ensaminadin-pe/walker/walker_firmware/kinematic.h

#ifndef KINEMATIC_H
#define KINEMATIC_H

#include "types.h"

enum KinematicAxis : uint8
{
	KINEMATIC_AXIS_UNDEFINED = 0,
	KINEMATIC_AXIS_X,
	KINEMATIC_AXIS_Y,
	KINEMATIC_AXIS_Z,
};

#endif // KINEMATIC_H
