ensaminadin-pe/walker/walker_firmware/fabrik2d.cpp

/**********************************************************************************************
 * FABRIK 2D inverse kinematics solver - Version 1.0.0
 * by Henrik Söderlund <henrik.a.soderlund@gmail.com>
 *
 * Copyright (C) 2018 Henrik Söderlund
 *
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
 **********************************************************************************************/

#ifndef IS_QT
	#include "Arduino.h"
#else
	#include "arduinopolyfill.h"
	#include <math.h>
#endif
#include "fabrik2d.h"
#include "kinematic.h"
#include "config.h"
#include <stdio.h>
#include <stdlib.h>

Fabrik2D::Fabrik2D(float _tolerance)
{
	tolerance = _tolerance; //1mm
	joint_count = 0;
	chain_length = 0;
	joint_chain = NULL;
	joints_axis = KINEMATIC_AXIS_UNDEFINED;
}

Fabrik2D::~Fabrik2D()
{

}

/**
 * @brief Fabrik2D::addJoint Add a joint to the kinematic chain
 * @param joint
 * @return
 */
bool Fabrik2D::addJoint(WalkerJoint *joint)
{
	//1) Check that the chain exist
	if (!joint_chain)
	{ //Create chain and last point
		joint_chain = (WalkerJoint**)malloc(sizeof(WalkerJoint*));
		if (!joint_chain) // Could not allocate memory, error
			return false;
		WalkerJoint* last_joint = new WalkerJoint();
		if (!last_joint)
			return false;
		joint_chain[0] = last_joint;
		joint_count = 1;
	}

	//2) Check that joint can be added
	if (joints_axis != KINEMATIC_AXIS_UNDEFINED && joint->getAxis() != joints_axis)
		return false; //Cannot add a joint that doesnt rotate on the same axis as the others, this is 2D Fabrik
	joints_axis = joint->getAxis();

	//3) Resize joint chain
	uint8 joint_index = joint_count++ - 1;
	joint_chain = (WalkerJoint**)realloc(joint_chain, joint_count * sizeof(WalkerJoint*));
	if (!joint_chain)
		return false;

	//4) Store new joint in chain at correct spot
	joint_chain[joint_count - 1] = joint_chain[joint_index];		//Last joint is currently at the new joint position, move it
	joint_chain[joint_index] = joint;								//Set new joint at its correct position : one before last

	//5) Rebuild joint position for new joint and last joint
	if (joint_index > 0) //Origin is at 0;0, no need to check it
	{
		placeNextJoint(joint_chain[joint_index - 1], joint); //Update positon x;y of our new joint
		placeNextJoint(joint_chain[joint_index], joint_chain[joint_index + 1]); //Update positon x;y of last joint
	}

	//6) Increase chain lenght
	chain_length += joint->getKinematicDistance();

	return true;
}

/**
 * @brief Fabrik2D::getJoint Get loaded joint at target index
 * @param joint_index
 * @return
 */
WalkerJoint *Fabrik2D::getJoint(uint8 joint_index)
{
	if (!joint_chain || joint_index < joint_count - 1 || !joint_chain[joint_count])
		return NULL;
	return joint_chain[joint_count];
}

/**
 * @brief Fabrik2D::reachFor Main resolution function
 * @param target_x
 * @param target_y
 * @return
 */
bool Fabrik2D::reachFor(float target_x, float target_y)
{
	///The basics of FABRIK
	/// http://www.andreasaristidou.com/publications/papers/FABRIK.pdf
	///  1) Check that the target point iw reachable by checking the full length of the chain
	///		If not, our program will move every joint points on a straight line toward the target
	///  2) If the distance can be reached, we need to recalculate the point positions of each joints on the 2D plane
	///     This is done in two stages :
	///		2.1) Backward search
	///			Start by moving the last point (n) of the chain on the target point itself.
	///			Then we need to find a line that passes threw n and n-1, and move n-1 on that line
	///			to the predefined joint distance in n-1, this will be the new positions of n-1.
	///			We repeat this process between n-1 and n-2, and so on until we reach the first point.
	///			But at this point, the first point of the chain is not at the origin anymore, so we need stage 2.
	///		2.2) Forward search
	///			Now we do exactly the same thing as before, but forward
	///			Move the first point of the chain (n) to the origin (0, 0).
	///			move n+1 on a line between n and n+1 to match the predefined distance between n and n+1.
	///			Do that for every points on your chain.
	///			Now our endpoint should be very close of the target point, but maybe a little bit too off,
	///			we can repeat the whole procedure to put it even closer, but reaching the point exactly might
	///			be a little bit too hard for the program, so add a little tolerance.
	///  3) Now you have a series of points on a 2d plane, you can calculate the angles between
	///     the differents vectors, giving you the angles of the joints
	if (joint_count < 2) //Nothing to do with that
		return false;

	//1) Check whether the target is within reach
	if (chain_length < get2dDistance(0, 0, target_x, target_y))
	{ // The target is unreachable, move every joint position in a straight line towards it
		for (uint8 i = 0; i == 0 || i < joint_count - 2; i++)
			relocateJoint(joint_chain[i], target_x, target_y, joint_chain[i]->getKinematicDistance());
	}
	else
	{//2) Target is reachable

		for (uint8 iteration = 0; iteration < FABRIK2D_MAX_ITERATIONS; iteration++)
		{ //Execute the algorithm a maximum of X times
			//2.1) Stage 1 : Backward search - move points from last to first
			// - Move last point on the target point
			joint_chain[joint_count - 1]->setKinematicPosition(target_x, target_y);
			// - Update every joints, starting from the one before last and going backward
			// - Relocate each joints to a point between their current location and their next joint location
			for (int i = joint_count - 2; i >= 0; i--)
				relocateJoint(joint_chain[i], joint_chain[i + 1]->getPlaneX(), joint_chain[i + 1]->getPlaneY(), joint_chain[i]->getKinematicDistance());

			//2.2) Stage 2 : Forward search - move points from first to last
			// - Move first point to the origin point
			joint_chain[0]->setKinematicPosition(0.0f, 0.0f);
			// - Update every joints, starting from the second and going forward
			// - Relocate each joints to a point between their current location and their previous joint location
			for (int i = 1; i < joint_count; i++)
				relocateJoint(joint_chain[i], joint_chain[i - 1]->getPlaneX(), joint_chain[i - 1]->getPlaneY(), joint_chain[i - 1]->getKinematicDistance());

			//2.3) Check distance between last point and target point
			if (get2dDistance(joint_chain[joint_count - 1]->getPlaneX(), joint_chain[joint_count - 1]->getPlaneY(), target_x, target_y) <= tolerance)
				break; //Last point is withing tolerable range of the target point, stop looking
			else
				tolerance += (tolerance * FABRIK2D_TOLERANCE_INCREASE); //Not close enought, increase tolerance a little
		}
	}

	//3) Update joint target angles in the chains
	updateJointAngles();

	return true;
}

/**
 * @brief Fabrik2D::setTolerance Change the tolerance
 * @param _tolerance
 */
void Fabrik2D::setTolerance(float _tolerance)
{
	if (_tolerance < 0.0f)
		_tolerance = 0.0f; //Not very tolerant of you
	tolerance = _tolerance;
}

void Fabrik2D::printChain()
{
	for (uint8 i = 0; i < joint_count; i++)
		printf("%u %f %f;%f\n", i, joint_chain[i]->getKinematicDistance(), joint_chain[i]->getPlaneX(), joint_chain[i]->getPlaneY());
}

/**
 * @brief Fabrik2D::updateJointAngles Update target angles in joints using current chain coordinates
 */
void Fabrik2D::updateJointAngles()
{
	if (joint_count < 2)
		return;

	for (uint8 i = 0; i < joint_count - 1; i++)
		joint_chain[i]->setTargetPosition(computeAngleForJoint(i));
}

/**
 * @brief Fabrik2D::clearChain Cleanup our chain in memory
 */
void Fabrik2D::clearChain()
{
	if (!joint_chain)
		return;

	//Just free the chain, the joints are freed elsewhere
	free(joint_chain);
	joint_chain = NULL;
}

/**
 * @brief Fabrik2D::get2dDistance Get distance between two points
 * @param x1
 * @param y1
 * @param x2
 * @param y2
 * @return
 */
float Fabrik2D::get2dDistance(float x1, float y1, float x2, float y2)
{
	float x_diff = x2 - x1;
	float y_diff = y2 - y1;
	return sqrt((x_diff * x_diff) + (y_diff * y_diff));
}

/**
 * @brief Fabrik2D::placeNextJoint Set default position of target joint from source joint using predefined distance and source position
 * @param source
 * @param target
 */
void Fabrik2D::placeNextJoint(WalkerJoint *source, WalkerJoint *target)
{
	target->setPlaneX(source->getPlaneX() + (source->getKinematicDistance() * cos(source->getBaseAngle())));
	target->setPlaneY(source->getPlaneY() + (source->getKinematicDistance() * sin(source->getBaseAngle())));
}

/**
 * @brief Fabrik2D::replaceJoint Move given joint position from its current position to the given distance on a line between its current position and the gien x/y coordinates
 * @param joint
 * @param target_x
 * @param target_y
 * @param distance
 */
void Fabrik2D::relocateJoint(WalkerJoint *joint, float target_x, float target_y, float distance)
{
	//1) Get distance between joint and point
	float current_distance = get2dDistance(joint->getPlaneX(), joint->getPlaneY(), target_x, target_y);

	//2) Get distance ratio between current distance and required new distance
	float distance_ratio = distance / current_distance;

	//3) Use the ratio to relocate joint point
	joint->setPlaneX(((1.0f - distance_ratio) * target_x) + (distance_ratio * joint->getPlaneX()));
	joint->setPlaneY(((1.0f - distance_ratio) * target_y) + (distance_ratio * joint->getPlaneY()));
}

/**
 * @brief Fabrik2D::computeAngleFor Get angle between three points in degrees
 * @param ax
 * @param ay
 * @param bx
 * @param by
 * @param cx
 * @param cy
 * @return
 */
float Fabrik2D::computeAngleFor(float ax, float ay, float bx, float by, float cx, float cy)
{ //https://stackoverflow.com/a/3487062
	//1) Calculate vectors AB and CB
	float ab_x = bx - ax;
	float ab_y = by - ay;
	float cb_x = bx - cx;
	float cb_y = by - cy;

	//2) Get angle between the three points in radian
	float radian_angle = atan2((ab_x * cb_y - ab_y * cb_x), (ab_x * cb_x + ab_y * cb_y));

	//3) Return angle in degrees
	return (radian_angle * 180.0f / 3.14f + 0.5f);
}

/**
 * @brief Fabrik2D::computeAngleFor Compute an angle for a target joint
 * @param joint_index
 * @return
 */
float Fabrik2D::computeAngleForJoint(uint8 joint_index)
{
	//1) Check that we can get the angle
	if (joint_index >= joint_count - 1)
		return 0.0f;

	//2) Get points
	float previous_x = 0.0f;
	float previous_y = 0.0f;
	WalkerJoint* current = joint_chain[joint_index];		//point B
	WalkerJoint* next = joint_chain[joint_index + 1];		//point C

	if (joint_index == 0)
	{ //Handle first joint
		//First joint default angle is 90° : every points are on the Y axis.
		//to get our angle, we use a fake point on the Y axis
		previous_x = 0.0f;
		previous_y = 300.0f;
	}
	else
	{ //Handle other joints
		WalkerJoint* previous = joint_chain[joint_index - 1];	//point A
		if (!previous)
			return 0.0f;
		previous_x = previous->getPlaneX();
		previous_y = previous->getPlaneY();
	}

	if (!current || !next)
		return 0.0f;

	//3) Get angle
	float angle = computeAngleFor(previous_x, previous_y,
								  current->getPlaneX(), current->getPlaneY(),
								  next->getPlaneX(), next->getPlaneY()
								  );

	//4) Apply joint offset
	float base_angle = current->getBaseAngle();
	if (joints_axis == KINEMATIC_AXIS_X)
		base_angle = 90.0f;
	if (angle < base_angle)
	{
		if (angle > 0)
			angle = - (base_angle - angle);
		else
			angle += base_angle;
	}
	else if (angle > base_angle)
		angle -= base_angle;

	return angle;
}
