ensaminadin-pe/walker/walker_firmware/types.h

#ifndef TYPES_H
#define TYPES_H

typedef signed char			int8;
typedef unsigned char		uint8;
typedef signed short		int16;
typedef unsigned short		uint16;
#ifdef IS_QT
	typedef signed long			int32;
	typedef unsigned long		uint32;
#endif
typedef signed long long	int64;
typedef unsigned long long	uint64;

#endif // TYPES_H
